futureoceanlab/AudaciousCTD/code/Inc/flash.h

#ifdef __cplusplus
extern "C" {
#endif


#include "stm32f3xx_hal.h"

struct SensorData {
	uint32_t Idx;
	uint32_t Timestamp;
	float Pressure;
	float Temperature;
	float Conductivity;
};

#define SENSOR_DATA_N_VAR 				5
#define SENSOR_DATA_SIZE 				((uint32_t)sizeof(struct SensorData))
/* Start @ of user Flash area */
#define FLASH_USER_START_ADDR   		ADDR_FLASH_PAGE_20
/* End @ of user Flash area */
#define FLASH_USER_END_ADDR     		ADDR_FLASH_PAGE_254 + FLASH_PAGE_SIZE
#define FLASH_TOTAL_DATA_PAGES			((uint8_t) ((FLASH_USER_END_ADDR - FLASH_USER_START_ADDR) / FLASH_PAGE_SIZE))
#define FLASH_GLOBAL_DATA_IDX 			FLASH_GLOBAL_CONFIG_ADDR +  sizeof(uint32_t)
// I2C allows max 2^16 bits (2^13 bytes = 4 pages)
#define MAX_SENSOR_DATA_BYTES 			((uint16_t)(FLASH_PAGE_SIZE - (FLASH_PAGE_SIZE % SENSOR_DATA_SIZE)))
#define MAX_SENSOR_DATA_ARR_LEN 		((uint16_t)(MAX_SENSOR_DATA_BYTES/SENSOR_DATA_SIZE))

/* Base address of the Flash pages */
#define ADDR_FLASH_PAGE_0     ((uint32_t)0x08000000) /* Base @ of Page 0, 2 Kbytes */
#define ADDR_FLASH_PAGE_1     ((uint32_t)0x08000800) /* Base @ of Page 1, 2 Kbytes */
#define ADDR_FLASH_PAGE_2     ((uint32_t)0x08001000) /* Base @ of Page 2, 2 Kbytes */
#define ADDR_FLASH_PAGE_3     ((uint32_t)0x08001800) /* Base @ of Page 3, 2 Kbytes */
#define ADDR_FLASH_PAGE_4     ((uint32_t)0x08002000) /* Base @ of Page 4, 2 Kbytes */
#define ADDR_FLASH_PAGE_5     ((uint32_t)0x08002800) /* Base @ of Page 5, 2 Kbytes */
#define ADDR_FLASH_PAGE_6     ((uint32_t)0x08003000) /* Base @ of Page 6, 2 Kbytes */
#define ADDR_FLASH_PAGE_7     ((uint32_t)0x08003800) /* Base @ of Page 7, 2 Kbytes */
#define ADDR_FLASH_PAGE_8     ((uint32_t)0x08004000) /* Base @ of Page 8, 2 Kbytes */
#define ADDR_FLASH_PAGE_9     ((uint32_t)0x08004800) /* Base @ of Page 9, 2 Kbytes */
#define ADDR_FLASH_PAGE_10    ((uint32_t)0x08005000) /* Base @ of Page 10, 2 Kbytes */
#define ADDR_FLASH_PAGE_11    ((uint32_t)0x08005800) /* Base @ of Page 11, 2 Kbytes */
#define ADDR_FLASH_PAGE_12    ((uint32_t)0x08006000) /* Base @ of Page 12, 2 Kbytes */
#define ADDR_FLASH_PAGE_13    ((uint32_t)0x08006800) /* Base @ of Page 13, 2 Kbytes */
#define ADDR_FLASH_PAGE_14    ((uint32_t)0x08007000) /* Base @ of Page 14, 2 Kbytes */
#define ADDR_FLASH_PAGE_15    ((uint32_t)0x08007800) /* Base @ of Page 15, 2 Kbytes */
#define ADDR_FLASH_PAGE_16    ((uint32_t)0x08008000) /* Base @ of Page 16, 2 Kbytes */
#define ADDR_FLASH_PAGE_17    ((uint32_t)0x08008800) /* Base @ of Page 17, 2 Kbytes */
#define ADDR_FLASH_PAGE_18    ((uint32_t)0x08009000) /* Base @ of Page 18, 2 Kbytes */
#define ADDR_FLASH_PAGE_19    ((uint32_t)0x08009800) /* Base @ of Page 19, 2 Kbytes */
#define ADDR_FLASH_PAGE_20    ((uint32_t)0x0800A000) /* Base @ of Page 20, 2 Kbytes */
#define ADDR_FLASH_PAGE_21    ((uint32_t)0x0800A800) /* Base @ of Page 21, 2 Kbytes */
#define ADDR_FLASH_PAGE_22    ((uint32_t)0x0800B000) /* Base @ of Page 22, 2 Kbytes */
#define ADDR_FLASH_PAGE_23    ((uint32_t)0x0800B800) /* Base @ of Page 23, 2 Kbytes */
#define ADDR_FLASH_PAGE_24    ((uint32_t)0x0800C000) /* Base @ of Page 24, 2 Kbytes */
#define ADDR_FLASH_PAGE_25    ((uint32_t)0x0800C800) /* Base @ of Page 25, 2 Kbytes */
#define ADDR_FLASH_PAGE_26    ((uint32_t)0x0800D000) /* Base @ of Page 26, 2 Kbytes */
#define ADDR_FLASH_PAGE_27    ((uint32_t)0x0800D800) /* Base @ of Page 27, 2 Kbytes */
#define ADDR_FLASH_PAGE_28    ((uint32_t)0x0800E000) /* Base @ of Page 28, 2 Kbytes */
#define ADDR_FLASH_PAGE_29    ((uint32_t)0x0800E800) /* Base @ of Page 29, 2 Kbytes */
#define ADDR_FLASH_PAGE_30    ((uint32_t)0x0800F000) /* Base @ of Page 30, 2 Kbytes */
#define ADDR_FLASH_PAGE_31    ((uint32_t)0x0800F800) /* Base @ of Page 31, 2 Kbytes */
#define ADDR_FLASH_PAGE_32    ((uint32_t)0x08010000) /* Base @ of Page 32, 2 Kbytes */
#define ADDR_FLASH_PAGE_33    ((uint32_t)0x08010800) /* Base @ of Page 33, 2 Kbytes */
#define ADDR_FLASH_PAGE_34    ((uint32_t)0x08011000) /* Base @ of Page 34, 2 Kbytes */
#define ADDR_FLASH_PAGE_35    ((uint32_t)0x08011800) /* Base @ of Page 35, 2 Kbytes */
#define ADDR_FLASH_PAGE_36    ((uint32_t)0x08012000) /* Base @ of Page 36, 2 Kbytes */
#define ADDR_FLASH_PAGE_37    ((uint32_t)0x08012800) /* Base @ of Page 37, 2 Kbytes */
#define ADDR_FLASH_PAGE_38    ((uint32_t)0x08013000) /* Base @ of Page 38, 2 Kbytes */
#define ADDR_FLASH_PAGE_39    ((uint32_t)0x08013800) /* Base @ of Page 39, 2 Kbytes */
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
#define ADDR_FLASH_PAGE_224   ((uint32_t)0x08070000) /* Base @ of Page 224, 2 Kbytes */
#define ADDR_FLASH_PAGE_225   ((uint32_t)0x08070800) /* Base @ of Page 225, 2 Kbytes */
#define ADDR_FLASH_PAGE_226   ((uint32_t)0x08071000) /* Base @ of Page 226, 2 Kbytes */
#define ADDR_FLASH_PAGE_227   ((uint32_t)0x08071800) /* Base @ of Page 227, 2 Kbytes */
#define ADDR_FLASH_PAGE_228   ((uint32_t)0x08072000) /* Base @ of Page 228, 2 Kbytes */
#define ADDR_FLASH_PAGE_229   ((uint32_t)0x08072800) /* Base @ of Page 229, 2 Kbytes */
#define ADDR_FLASH_PAGE_230   ((uint32_t)0x08073000) /* Base @ of Page 230, 2 Kbytes */
#define ADDR_FLASH_PAGE_231   ((uint32_t)0x08073800) /* Base @ of Page 231, 2 Kbytes */
#define ADDR_FLASH_PAGE_232   ((uint32_t)0x08074000) /* Base @ of Page 232, 2 Kbytes */
#define ADDR_FLASH_PAGE_233   ((uint32_t)0x08074800) /* Base @ of Page 233, 2 Kbytes */
#define ADDR_FLASH_PAGE_234   ((uint32_t)0x08075000) /* Base @ of Page 234, 2 Kbytes */
#define ADDR_FLASH_PAGE_235   ((uint32_t)0x08075800) /* Base @ of Page 235, 2 Kbytes */
#define ADDR_FLASH_PAGE_236   ((uint32_t)0x08076000) /* Base @ of Page 236, 2 Kbytes */
#define ADDR_FLASH_PAGE_237   ((uint32_t)0x08076800) /* Base @ of Page 237, 2 Kbytes */
#define ADDR_FLASH_PAGE_238   ((uint32_t)0x08077000) /* Base @ of Page 238, 2 Kbytes */
#define ADDR_FLASH_PAGE_239   ((uint32_t)0x08077800) /* Base @ of Page 239, 2 Kbytes */
#define ADDR_FLASH_PAGE_240   ((uint32_t)0x08078000) /* Base @ of Page 240, 2 Kbytes */
#define ADDR_FLASH_PAGE_241   ((uint32_t)0x08078800) /* Base @ of Page 241, 2 Kbytes */
#define ADDR_FLASH_PAGE_242   ((uint32_t)0x08079000) /* Base @ of Page 242, 2 Kbytes */
#define ADDR_FLASH_PAGE_243   ((uint32_t)0x08079800) /* Base @ of Page 243, 2 Kbytes */
#define ADDR_FLASH_PAGE_244   ((uint32_t)0x0807a000) /* Base @ of Page 244, 2 Kbytes */
#define ADDR_FLASH_PAGE_245   ((uint32_t)0x0807a800) /* Base @ of Page 245, 2 Kbytes */
#define ADDR_FLASH_PAGE_246   ((uint32_t)0x0807b000) /* Base @ of Page 246, 2 Kbytes */
#define ADDR_FLASH_PAGE_247   ((uint32_t)0x0807b800) /* Base @ of Page 247, 2 Kbytes */
#define ADDR_FLASH_PAGE_248   ((uint32_t)0x0807c000) /* Base @ of Page 248, 2 Kbytes */
#define ADDR_FLASH_PAGE_249   ((uint32_t)0x0807c800) /* Base @ of Page 249, 2 Kbytes */
#define ADDR_FLASH_PAGE_250   ((uint32_t)0x0807d000) /* Base @ of Page 250, 2 Kbytes */
#define ADDR_FLASH_PAGE_251   ((uint32_t)0x0807d800) /* Base @ of Page 251, 2 Kbytes */
#define ADDR_FLASH_PAGE_252   ((uint32_t)0x0807e000) /* Base @ of Page 252, 2 Kbytes */
#define ADDR_FLASH_PAGE_253   ((uint32_t)0x0807e800) /* Base @ of Page 253, 2 Kbytes */
#define ADDR_FLASH_PAGE_254   ((uint32_t)0x0807f000) /* Base @ of Page 254, 2 Kbytes */
#define ADDR_FLASH_PAGE_255   ((uint32_t)0x0807f800) /* Base @ of Page 255, 2 Kbytes */


struct SensorData s_data_array[MAX_SENSOR_DATA_ARR_LEN];

uint16_t Flash_Get_Nth_Page(uint8_t page);
uint32_t Flash_Get_Page_Addr(uint8_t page);
int8_t Flash_Erase(uint32_t start_addr, uint32_t end_addr, uint32_t n);
void Flash_Save_Bulk_Data(struct SensorData *bulk_data, uint8_t len,
							uint8_t page, uint16_t global_nth_page);
uint32_t Flash_Write_Sensor_Data(uint32_t start_addr, uint32_t end_addr,
								struct SensorData *s);
void Flash_Read_Page_Sensor_Data(uint8_t page, struct SensorData s_data[], uint32_t len);
uint32_t Flash_Read_Sensor_Data(uint32_t start_addr, struct SensorData *s_data);



#ifdef __cplusplus
}
#endif
