futureoceanlab/AudaciousCTD/code/Inc/I2C.h

#ifdef __cplusplus
extern "C" {
#endif


#include "stm32f3xx_hal.h"


I2C_HandleTypeDef hi2c1;
I2C_HandleTypeDef hi2c2;


void MX_I2C1_Init(void);
void MX_I2C2_Init(void);

#ifdef __cplusplus
}
#endif
