futureoceanlab/AudaciousCTD/code/Inc/timer.h

#ifdef __cplusplus
extern "C" {
#endif

#include "stm32f3xx_hal.h"

void MX_TIM2_Init(void);
void MX_TIM3_Init(void);
void MX_TIM4_Init(void);

TIM_HandleTypeDef htim2;
TIM_HandleTypeDef htim3;
TIM_HandleTypeDef htim4;



#ifdef __cplusplus
}
#endif
